MoJoKi42/flipControl/FlipDot_BROSE_LAWO/Inc/6x8_vertikal_LSB_1.h

const char font_6x8vertikal_LSB[256][6]={
{0x00,0x00,0x00,0x00,0x00,0x00},	// 0x00
{0x00,0x3E,0x45,0x51,0x45,0x3E},	// 0x01
{0x00,0x3E,0x6B,0x6F,0x6B,0x3E},	// 0x02
{0x00,0x1C,0x3E,0x7C,0x3E,0x1C},	// 0x03
{0x00,0x18,0x3C,0x7E,0x3C,0x18},	// 0x04
{0x00,0x30,0x36,0x7F,0x36,0x30},	// 0x05
{0x00,0x18,0x5C,0x7E,0x5C,0x18},	// 0x06
{0x00,0x00,0x00,0x00,0x00,0x00},	// 0x07
{0x00,0x00,0x00,0x00,0x00,0x00},	// 0x08
{0x00,0x00,0x00,0x00,0x00,0x00},	// 0x09
{0x00,0x00,0x00,0x00,0x00,0x00},	// 0x0A
{0x00,0x30,0x48,0x4A,0x36,0x0E},	// 0x0B
{0x00,0x06,0x29,0x79,0x29,0x06},	// 0x0C
{0x00,0x00,0x00,0x00,0x00,0x00},	// 0x0D
{0x00,0x60,0x7E,0x0A,0x35,0x3F},	// 0x0E
{0x00,0x2A,0x1C,0x36,0x1C,0x2A},	// 0x0F
{0x00,0x00,0x7F,0x3E,0x1C,0x08},	// 0x10
{0x00,0x08,0x1C,0x3E,0x7F,0x00},	// 0x11
{0x00,0x14,0x36,0x7F,0x36,0x14},	// 0x12
{0x00,0x00,0x5F,0x00,0x5F,0x00},	// 0x13
{0x00,0x06,0x09,0x7F,0x01,0x7F},	// 0x14
{0x00,0x22,0x4D,0x55,0x59,0x22},	// 0x15
{0x00,0x60,0x60,0x60,0x60,0x00},	// 0x16
{0x00,0x14,0xB6,0xFF,0xB6,0x14},	// 0x17
{0x00,0x04,0x06,0x7F,0x06,0x04},	// 0x18
{0x00,0x10,0x30,0x7F,0x30,0x10},	// 0x19
{0x00,0x08,0x08,0x3E,0x1C,0x08},	// 0x1A
{0x00,0x08,0x1C,0x3E,0x08,0x08},	// 0x1B
{0x00,0x78,0x40,0x40,0x40,0x40},	// 0x1C
{0x00,0x08,0x3E,0x08,0x3E,0x08},	// 0x1D
{0x00,0x30,0x3C,0x3F,0x3C,0x30},	// 0x1E
{0x00,0x03,0x0F,0x3F,0x0F,0x03},	// 0x1F
{0x00,0x00,0x00,0x00,0x00,0x00},	// 0x20
{0x00,0x00,0x06,0x5F,0x06,0x00},	// 0x21
{0x00,0x07,0x03,0x00,0x07,0x03},	// 0x22
{0x00,0x24,0x7E,0x24,0x7E,0x24},	// 0x23
{0x00,0x24,0x2B,0x6A,0x12,0x00},	// 0x24
{0x00,0x63,0x13,0x08,0x64,0x63},	// 0x25
{0x00,0x36,0x49,0x56,0x20,0x50},	// 0x26
{0x00,0x00,0x07,0x03,0x00,0x00},	// 0x27
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
};
