MoJoKi42/flipControl/FlipDot_BROSE_LAWO/Inc/fnt8x8.h

#ifndef _FNT_8x8_H
#define _FNT_8x8_H
#include <inttypes.h>
#ifdef AVR_BUILD
#include <avr/pgmspace.h>
const PROGMEM uint8_t font8x8int[]={
#else
const uint8_t font8x8int[]={
#endif
	0x00, 0x00, 0x00, 0x00, 0x00, 0x00, 0x00, 0x00,
	 0x7e, 0x81, 0x95, 0xb1, 0xb1, 0x95, 0x81, 0x7e,
	 0x7e, 0xff, 0xeb, 0xcf, 0xcf, 0xeb, 0xff, 0x7e,
	 0x0e, 0x1f, 0x3f, 0x7e, 0x3f, 0x1f, 0x0e, 0x00,
	 0x08, 0x1c, 0x3e, 0x7f, 0x3e, 0x1c, 0x08, 0x00,
	 0x38, 0x3a, 0x9f, 0xff, 0x9f, 0x3a, 0x38, 0x00,
	 0x10, 0x38, 0xbc, 0xff, 0xbc, 0x38, 0x10, 0x00,
	 0x00, 0x00, 0x18, 0x3c, 0x3c, 0x18, 0x00, 0x00,
	 0xff, 0xff, 0xe7, 0xc3, 0xc3, 0xe7, 0xff, 0xff,
	 0x00, 0x3c, 0x66, 0x42, 0x42, 0x66, 0x3c, 0x00,
	 0xff, 0xc3, 0x99, 0xbd, 0xbd, 0x99, 0xc3, 0xff,
	 0x70, 0xf8, 0x88, 0x88, 0xfd, 0x7f, 0x07, 0x0f,
	 0x00, 0x4e, 0x5f, 0xf1, 0xf1, 0x5f, 0x4e, 0x00,
	 0xc0, 0xe0, 0xff, 0x7f, 0x05, 0x05, 0x07, 0x07,
	 0xc0, 0xff, 0x7f, 0x05, 0x05, 0x65, 0x7f, 0x3f,
	 0x5a, 0x5a, 0x3c, 0xe7, 0xe7, 0x3c, 0x5a, 0x5a,
	 0x7f, 0x3e, 0x3e, 0x1c, 0x1c, 0x08, 0x08, 0x00,
	 0x08, 0x08, 0x1c, 0x1c, 0x3e, 0x3e, 0x7f, 0x00,
	 0x00, 0x24, 0x66, 0xff, 0xff, 0x66, 0x24, 0x00,
	 0x00, 0x5f, 0x5f, 0x00, 0x00, 0x5f, 0x5f, 0x00,
	 0x06, 0x0f, 0x09, 0x7f, 0x7f, 0x01, 0x7f, 0x7f,
	 0x40, 0xda, 0xbf, 0xa5, 0xfd, 0x59, 0x03, 0x02,
	 0x00, 0x70, 0x70, 0x70, 0x70, 0x70, 0x70, 0x00,
	 0x80, 0x94, 0xb6, 0xff, 0xff, 0xb6, 0x94, 0x80,
	 0x00, 0x04, 0x06, 0x7f, 0x7f, 0x06, 0x04, 0x00,
	 0x00, 0x10, 0x30, 0x7f, 0x7f, 0x30, 0x10, 0x00,
	 0x08, 0x08, 0x08, 0x2a, 0x3e, 0x1c, 0x08, 0x00,
	 0x08, 0x1c, 0x3e, 0x2a, 0x08, 0x08, 0x08, 0x00,
	 0x3c, 0x3c, 0x20, 0x20, 0x20, 0x20, 0x20, 0x00,
	 0x08, 0x1c, 0x3e, 0x08, 0x08, 0x3e, 0x1c, 0x08,
	 0x30, 0x38, 0x3c, 0x3e, 0x3e, 0x3c, 0x38, 0x30,
	 0x06, 0x0e, 0x1e, 0x3e, 0x3e, 0x1e, 0x0e, 0x06,
	 0x00, 0x00, 0x00, 0x00, 0x00, 0x00, 0x00, 0x00,
	 0x00, 0x06, 0x5f, 0x5f, 0x06, 0x00, 0x00, 0x00,
	 0x00, 0x07, 0x07, 0x00, 0x07, 0x07, 0x00, 0x00,
	 0x14, 0x7f, 0x7f, 0x14, 0x7f, 0x7f, 0x14, 0x00,
	 0x24, 0x2e, 0x6b, 0x6b, 0x3a, 0x12, 0x00, 0x00,
	 0x46, 0x66, 0x30, 0x18, 0x0c, 0x66, 0x62, 0x00,
	 0x30, 0x7a, 0x4f, 0x5d, 0x37, 0x7a, 0x48, 0x00,
	 0x04, 0x07, 0x03, 0x00, 0x00, 0x00, 0x00, 0x00,
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
#endif
